TavranCode/KerbalKockpit/Prototype PCBs/Shield v.2/Shield v.2 - Copy.kicad_pcb

## KiCad design Prototype PCBs/Shield v.2/Shield v.2 - Copy.kicad_pcb (2020-02-17, an earlier design)

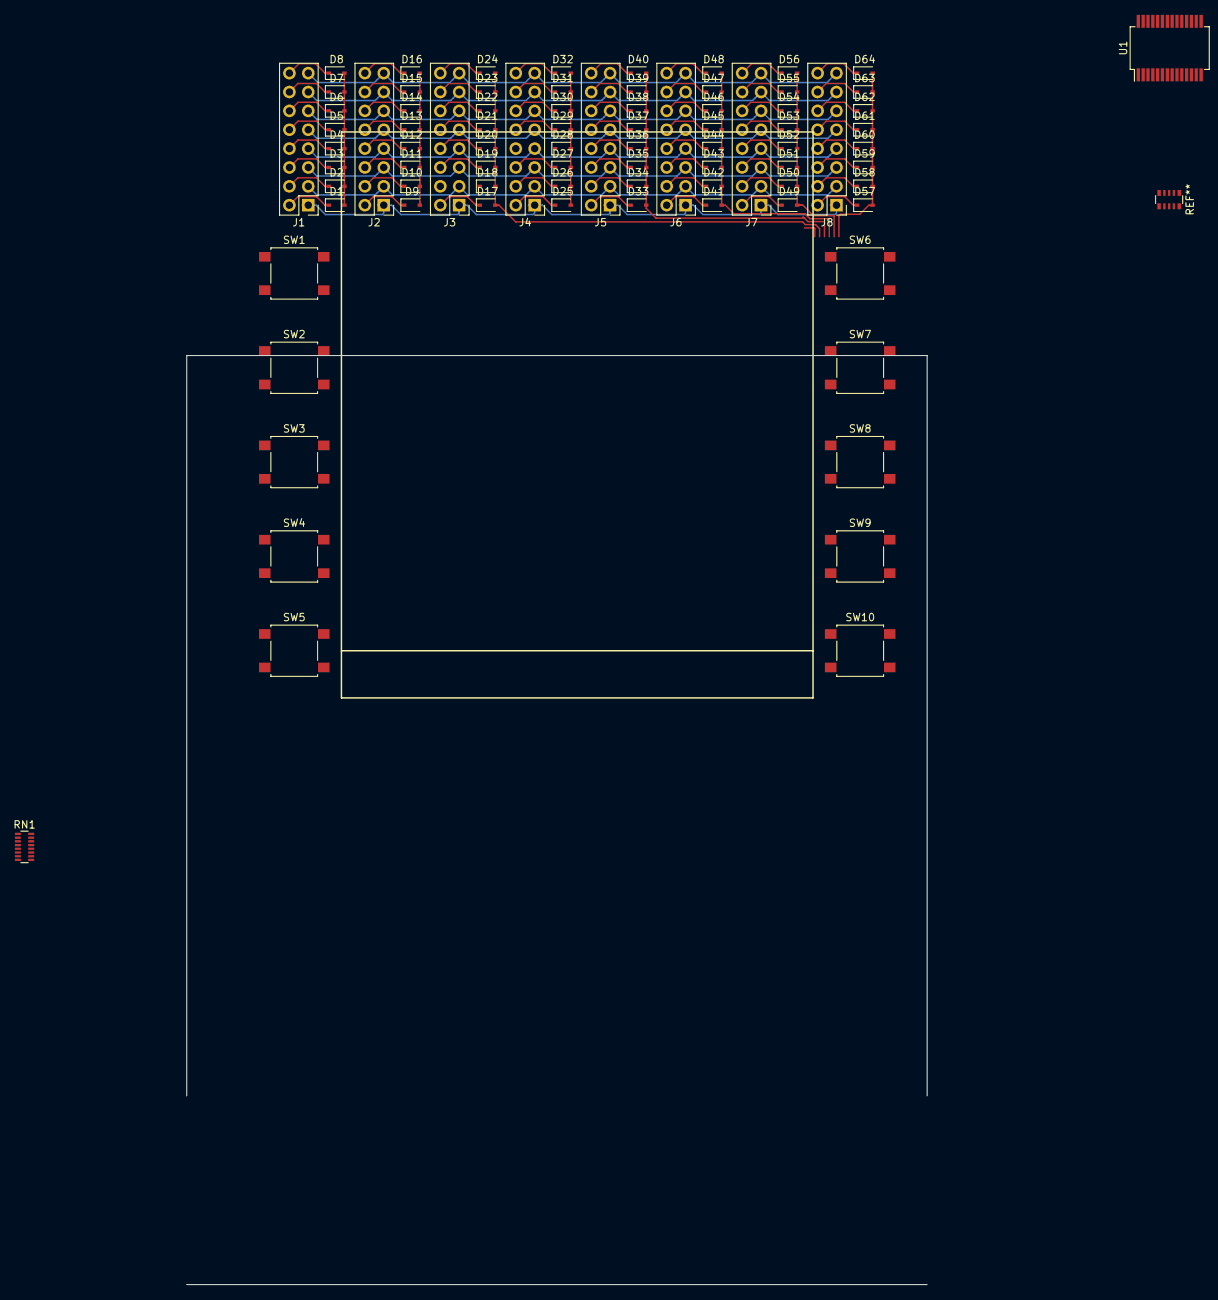
[picture p32: board Shield v.2 - Copy.kicad_pcb from above]

Board: 2 copper layers, 84 parts (0 on the bottom side), 80 nets.

Parts:
D1, D2, D3, D4, D5, D6, D7, D8, D9, D10, D11, D12, D13, D14, D15, D16, D17, D18, D19, D20, D21, D22, D23, D24, D25, D26, D27, D28, D29, D30, D31, D32, D33, D34, D35, D36, D37, D38, D39, D40, D41, D42, D43, D44, D45, D46, D47, D48, D49, D50, D51, D52, D53, D54, D55, D56, D57, D58, D59, D60, D61, D62, D63, D64: 1N4148; D_SOD-323
J1, J2, J3, J4, J5, J6, J7, J8: JumpSwitch; PinHeader_2x08_P2.54mm_Vertical
RN1: R_Network08_US; R_Array_Convex_8x0602
SW1, SW2, SW3, SW4, SW5, SW6, SW7, SW8, SW9, SW10: SW_Push; SW_SPST_B3S-1000
U1: MCP23017_SS; SSOP-28_5.3x10.2mm_P0.65mm

Connections:
/Input Matrix/input_c0: D1.2, D2.2, D6.2, D7.2, D8.2, U1.28
/Input Matrix/input_c1: D9.2, D10.2, D11.2, D12.2, D13.2, D14.2, D15.2, D16.2, U1.27
/Input Matrix/input_c2: D17.2, D18.2, D19.2, D20.2, D21.2, D22.2, D23.2, D24.2, U1.25
/Input Matrix/input_c3: D25.2, D26.2, D27.2, D28.2, D29.2, D30.2, D31.2, D32.2, U1.26
/Input Matrix/input_c4: D33.2, D34.2, D35.2, D36.2, D37.2, D38.2, D39.2, D40.2, U1.24
/Input Matrix/input_c5: D41.2, D42.2, D43.2, D44.2, D45.2, D46.2, D47.2, D48.2, U1.23
/Input Matrix/input_c6: D49.2, D50.2, D51.2, D52.2, D53.2, D54.2, D55.2, D56.2, U1.22
/Input Matrix/input_c7: D57.2, D58.2, D59.2, D60.2, D61.2, D62.2, D63.2, D64.2, U1.21
/Input Matrix/input_r0: J1.1, J2.1, J3.1, J4.1, J5.1, J6.1, J7.1, J8.1, RN1.2, SW1.1, SW6.1, U1.1
/Input Matrix/input_r1: J1.3, J2.3, J3.3, J4.3, J5.3, J6.3, J7.3, J8.3, RN1.3, SW2.1, SW7.1, U1.2
/Input Matrix/input_r2: J2.5, J3.5, J4.5, J5.5, J6.5, J7.5, J8.5, RN1.5, SW3.1, SW8.1, U1.4
/Input Matrix/input_r3: J2.7, J3.7, J4.7, J5.7, J6.7, J7.7, J8.7, RN1.4, SW4.1, SW9.1, U1.3
/Input Matrix/input_r4: J2.9, J3.9, J4.9, J5.9, J6.9, J7.9, J8.9, RN1.6, SW5.1, SW10.1, U1.5
/Input Matrix/input_r5: J1.11, J2.11, J3.11, J4.11, J5.11, J6.11, J7.11, J8.11, RN1.7, U1.6
/Input Matrix/input_r6: J1.13, J2.13, J3.13, J4.13, J5.13, J6.13, J7.13, J8.13, RN1.8, U1.7
/Input Matrix/input_r7: J1.15, J2.15, J3.15, J4.15, J5.15, J6.15, J7.15, J8.15, RN1.9, U1.8
unnamed: D1.1, J1.2, SW1.2
unnamed: D2.1, J1.4, SW2.2
unnamed: D3.1, J1.6, SW3.2
unnamed: D4.1, J1.8, SW4.2
unnamed: D5.1, J1.10, SW5.2
unnamed: D6.1, J1.12
unnamed: D7.1, J1.14
unnamed: D8.1, J1.16
unnamed: D9.1, J2.2
unnamed: D10.1, J2.4
unnamed: D11.1, J2.6
unnamed: D12.1, J2.8
unnamed: D13.1, J2.10
unnamed: D14.1, J2.12
unnamed: D15.1, J2.14
unnamed: D16.1, J2.16
unnamed: D17.1, J3.2
unnamed: D18.1, J3.4
unnamed: D19.1, J3.6
unnamed: D20.1, J3.8
unnamed: D21.1, J3.10
unnamed: D22.1, J3.12
unnamed: D23.1, J3.14
unnamed: D24.1, J3.16
unnamed: D25.1, J4.2
unnamed: D26.1, J4.4
unnamed: D27.1, J4.6
unnamed: D28.1, J4.8
unnamed: D29.1, J4.10
unnamed: D30.1, J4.12
unnamed: D31.1, J4.14
unnamed: D32.1, J4.16
unnamed: D33.1, J5.2
unnamed: D34.1, J5.4
unnamed: D35.1, J5.6
unnamed: D36.1, J5.8
unnamed: D37.1, J5.10
unnamed: D38.1, J5.12
unnamed: D39.1, J5.14
unnamed: D40.1, J5.16
unnamed: D41.1, J6.2
unnamed: D42.1, J6.4
unnamed: D43.1, J6.6
unnamed: D44.1, J6.8
unnamed: D45.1, J6.10
unnamed: D46.1, J6.12
unnamed: D47.1, J6.14
unnamed: D48.1, J6.16
unnamed: D49.1, J7.2
unnamed: D50.1, J7.4
unnamed: D51.1, J7.6
unnamed: D52.1, J7.8
unnamed: D53.1, J7.10
unnamed: D54.1, J7.12
unnamed: D55.1, J7.14
unnamed: D56.1, J7.16
unnamed: D57.1, J8.2, SW6.2
unnamed: D58.1, J8.4, SW7.2
unnamed: D59.1, J8.6, SW8.2
unnamed: D60.1, J8.8, SW9.2
unnamed: D61.1, J8.10, SW10.2
unnamed: D62.1, J8.12
unnamed: D63.1, J8.14
unnamed: D64.1, J8.16
