TavranCode/KerbalKockpit/Python Controller/Settings.py

# SETUP CONSTANTS
c_camera_angle_rate = 1
c_camera_dist_rate = 1
c_camera_map_dist_rate = 10
c_trim_mod_rate = 0.01
c_fctl_db = 0.1
c_fctl_fine = 0.5
c_loop_frame_rate = 0.1
c_cam_change_time = 3.0

c_screen_size_x = 1274
c_screen_size_y = 1274
c_screen_pos = "+1+1" #"+580-900"
c_notebook_size_y = 780
c_tab_size_y = 750


G_cam_change_timer = -1.0



msg_prefix = ('MSG', 'ERROR', 'CRITICAL ERROR')

#GUI Preferences
lightcolor = '#FFCC00'
darkcolor = '#FFB000'
defaultfont = 'Fixedsys'
