TavranCode/KerbalKockpit/Arduino Test Projects/MotorPWMTest/MotorPWMTest.ino

// Control the vibration of an ERM motor
// using PWM and a photoresistor. 

#include <Sparkfun_DRV2605L.h>
#include <Wire.h>

SFE_HMD_DRV2605L HMD;
const int analogInPin = A2;  // Analog input pin that the sensor is attached to
const int analogOutPin = 11; // Analog output pin that the Haptic Motor Driver is attached to

int sensorValue = 0;        // value read from the sensor
int outputValue = 0;        // value output to the PWM (analog out)


void setup() 
{
  HMD.begin();
  Serial.begin(9600);
  HMD.Mode(0x03); //PWM INPUT 
  HMD.MotorSelect(0x0A);
  HMD.Library(7); //change to 6 for LRA motors 

}
void loop() 
{

 // read the analog in value:
  sensorValue = analogRead(analogInPin);
  // map it to the range of the analog out:
  outputValue = map(sensorValue, 0, 1023, 127, 255);
  // change the analog out value:
  analogWrite(analogOutPin, outputValue);

  // print the results to the serial monitor:
  Serial.print("sensor = ");
  Serial.print(sensorValue);
  Serial.print("\t output = ");
  Serial.println(outputValue);

  // wait 2 milliseconds before the next loop
  // for the analog-to-digital converter to settle
  // after the last reading:
  delay(2);
 }
